BogdanBackend/Diplom/docs/ch4.md

# ЕКСПЕРИМЕНТАЛЬНЕ ВИПРОБУВАННЯ

У цьому розділі представлено практичні випробування, проведені з метою перевірки працездатності та ефективності використання програмно-визначеного радіо (SDR) для прийому та обробки радіосигналів у реальних умовах. Основна увага зосереджена на експериментах, які демонструють можливості сучасних SDR-приймачів і програмних засобів прийому та обробки аналогових і супутникових сигналів.

Використання гнучких програмно-апаратних платформ дає змогу реалізовувати прийом, фільтрацію, демодуляцію та збереження сигналів без потреби у складному радіоелектронному обладнанні. Такий підхід відкриває нові перспективи для навчання, досліджень і прикладних завдань, пов’язаних з аналізом радіочастотного спектра.

У рамках випробувань було реалізовано два експерименти: прийом аналогового сигналу за допомогою портативної рації та SDR-приймача, а також дистанційний прийом супутникового зображення за допомогою онлайн-сервісу WebSDR. Обидва сценарії показують, як за допомогою доступних інструментів можна реалізувати повноцінну систему радіоприйому, обробки та візуалізації сигналу.

<!-- подяка автору https://www.youtube.com/watch?v=IaThnn2r1no -->

## Прийом аналогового радіосигналу за допомогою портативної рації та SDR-приймача

Мета роботи: Дослідити процес прийому та обробки аналогового радіосигналу за допомогою SDR-приймача BladeRF і програмного забезпечення GNU Radio, перевірити можливість його демодуляції, виводу на аудіосистему та запису у файл.

Теоретичні відомості

SDR — це радіоприймач, у якому більшість функцій (демодуляція, фільтрація, декодування) реалізовано програмно. Це дозволяє змінювати параметри прийому та обробки сигналу без зміни апаратного забезпечення.

Частотна модуляція (Frequency Modulation, FM) використовується для передавання звукових сигналів, при якій частота несучої хвилі змінюється пропорційно амплітуді вхідного сигналу. FM має високу стійкість до шумів, тому широко застосовується в аналоговому радіомовленні.

GNU Radio — програмне середовище для створення радіосистем на базі SDR. Працює з різними апаратними пристроями, зокрема BladeRF, і дозволяє створювати блок-схеми обробки сигналу.

Ми використовували портативну рацію Baofeng як джерело сигналу для експерименту. Основні технічні характеристики цієї рації такі: вона працює у діапазонах VHF (136–174 МГц) та UHF (400–520 МГц), забезпечує вихідну потужність від 1 до 8 Вт, використовує частотну модуляцію (FM) і дозволяє програмувати до 200 каналів. Також пристрій підтримує двоканальний моніторинг (Dual Watch), має функцію VOX для активації передавання голосом і оснащений системою шумоподавлення на основі CTCSS/DCS.

Використане обладнання та програмне забезпечення

* Джерело сигналу: портативна рація Baofeng
* Приймач: SDR-пристрій BladeRF
* Програмне забезпечення: GNU Radio

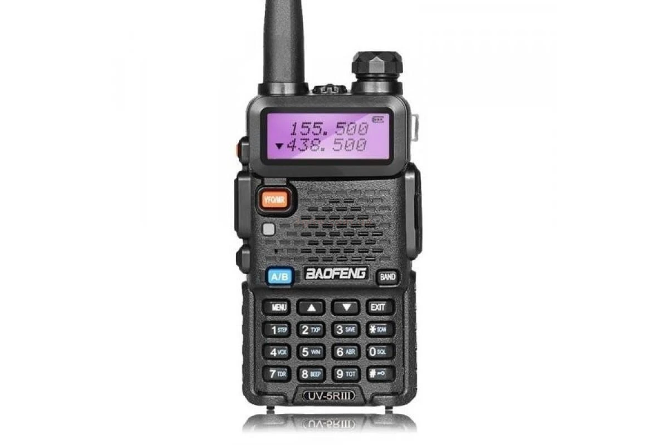
[picture p52: docs/imgs/image-35.png]
Рація Baofeng


Умови експерименту:

* Частота прийому: 446.13 МГц
* Частота дискретизації: задана у GNU Radio
* Посилення: мінімальне (–1)
* Вхідний блок: Osmocom Source (налаштований для BladeRF)

Блок-схема системи обробки сигналу:

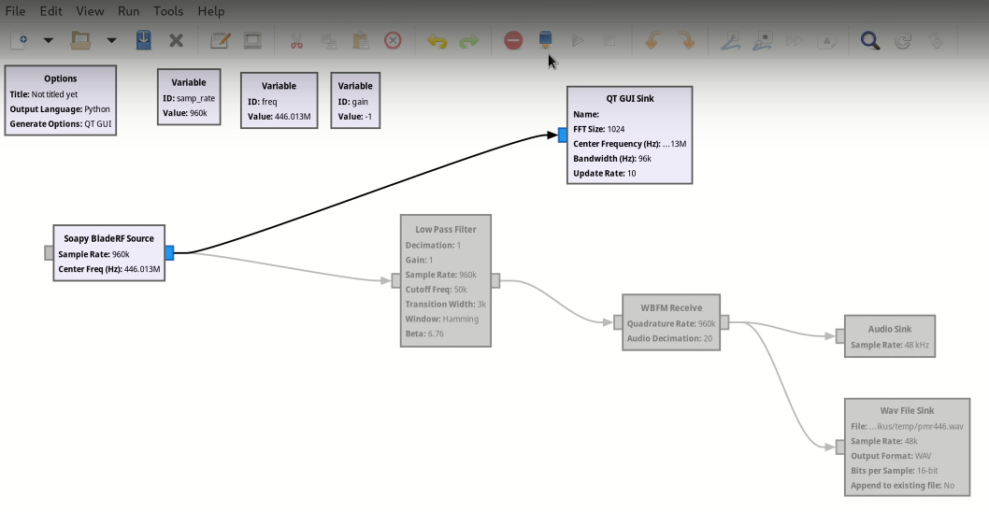
[picture p53: docs/imgs/image-36.png]
Структура цифрової обробки для графічного відображення


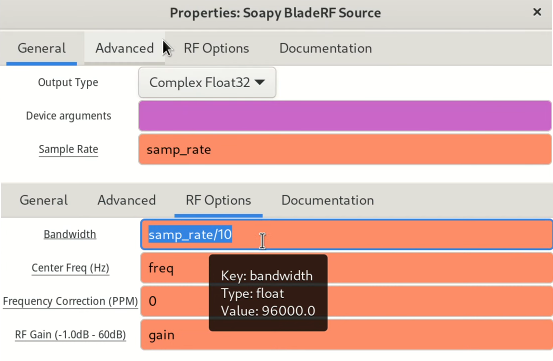
[picture p54: docs/imgs/image-37.png]
Параметри захоплення сигналу: частота, підсилення, ширина смуги пропускання


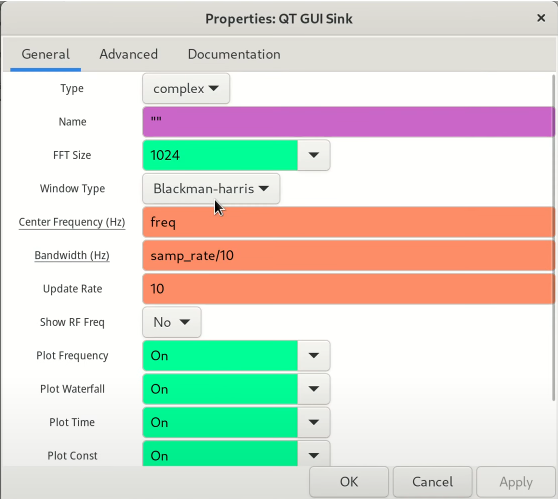
[picture p55: docs/imgs/image-38.png]
Параметри графічного відображення


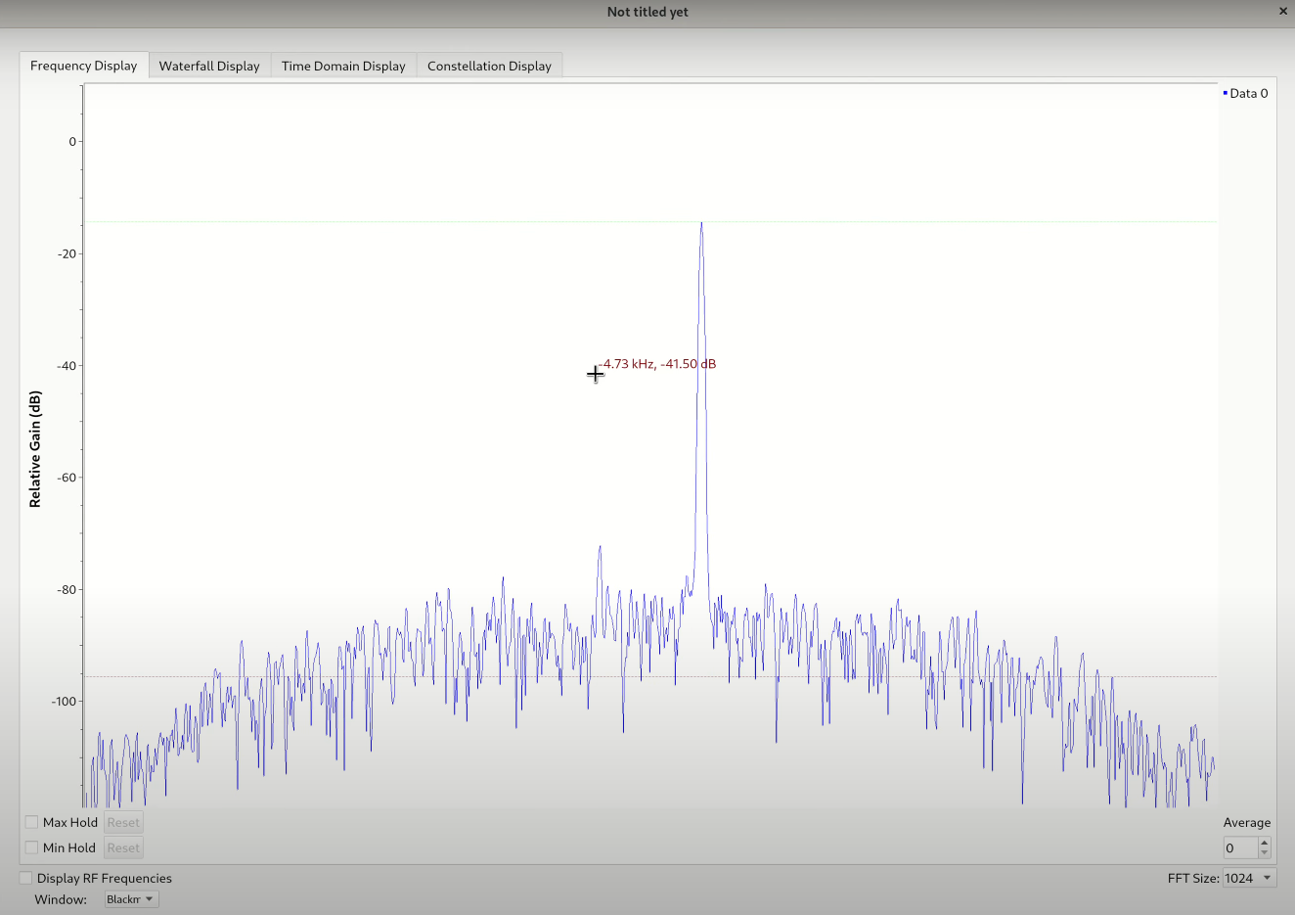
[picture p56: docs/imgs/image-39.png]
Спектр частот прийнятого сигналу


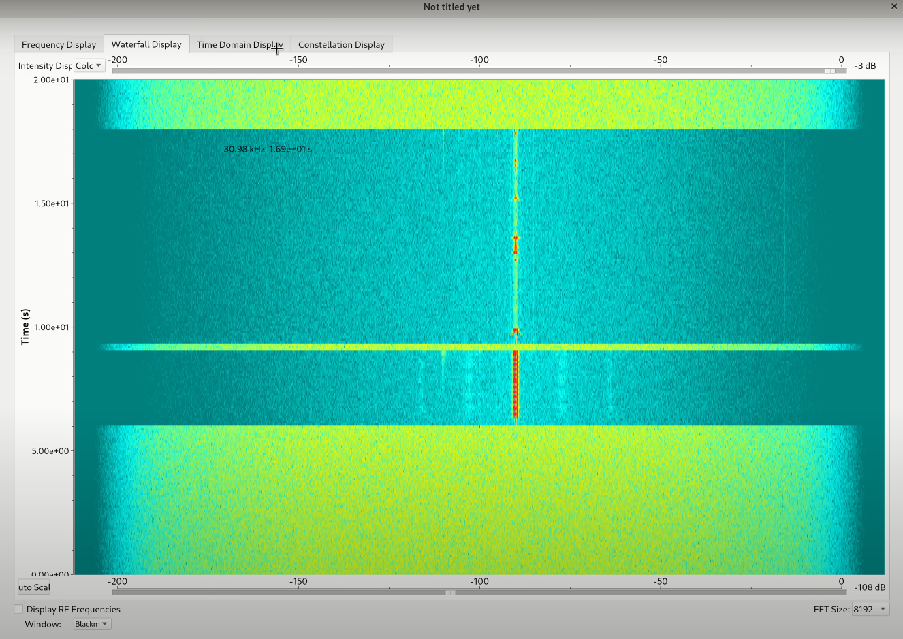
[picture p57: docs/imgs/image-40.png]
Динамічне водоспадне відображення прийнятого сигналу


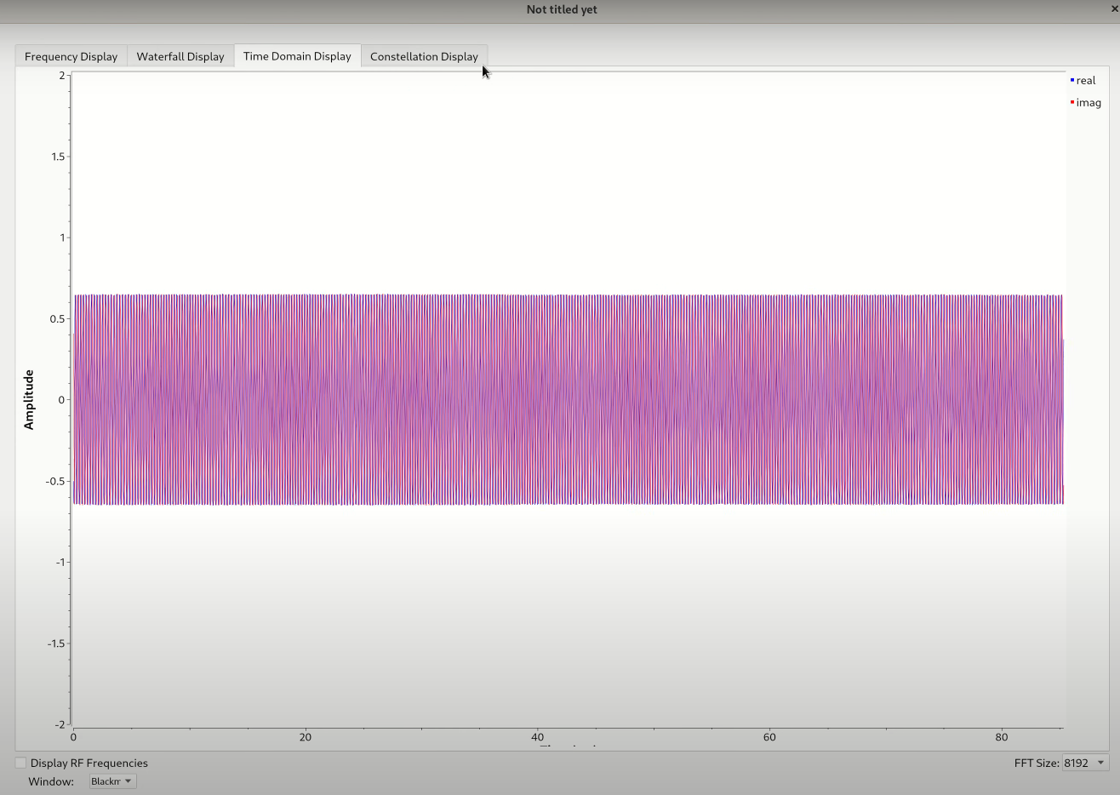
[picture p58: docs/imgs/image-41.png]
Амплітудне відображення прийнятого сигналу


<!-- ![Сузір’я прийнятого сигналу](imgs/image-42.png) -->

У процесі експерименту ми реалізували виведення сигналу на аудіосистему комп’ютера. Для цього до блок-схеми було додано фільтр низьких частот із частотою зрізу 50 кГц і перехідною зоною 3 кГц, блок демодуляції WBFM Receive із налаштуванням частоти дискретизації відповідно до потоку та параметром Audio Decimation, а також блок Audio Sink із частотою дискретизації 48000 Гц. Така конфігурація дала змогу якісно відтворити демодульований аудіосигнал у реальному часі.

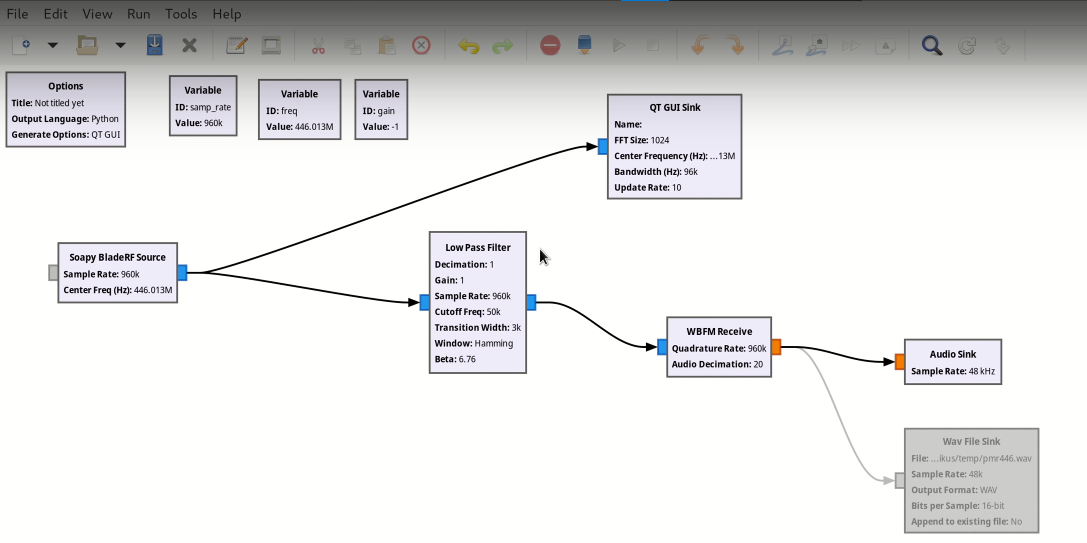
[picture p59: docs/imgs/image-43.png]
Структура цифрової обробки для аудіовиходу


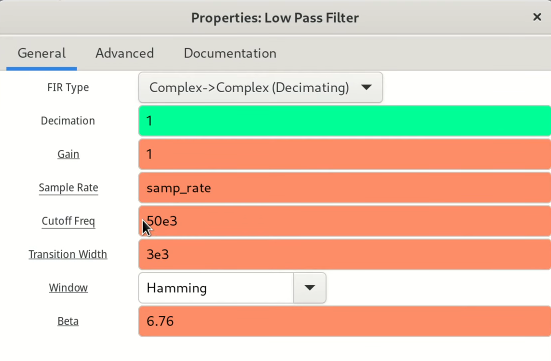
[picture p60: docs/imgs/image-44.png]
Налаштування фільтра низьких частот


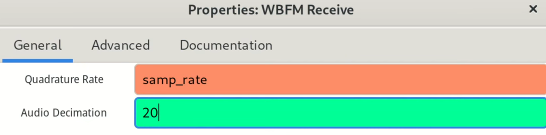
[picture p61: docs/imgs/image-45.png]
Налаштування FM демодулятора


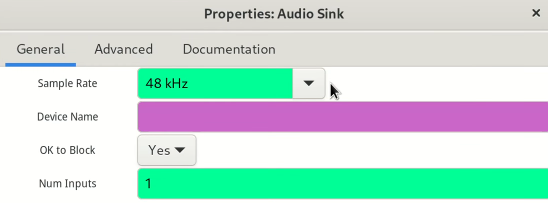
[picture p62: docs/imgs/image-46.png]
Налаштування аудіовиходу


Запис сигналу у WAV-файл ми здійснили шляхом заміни блоку Audio Sink на WAV File Sink у схемі обробки. Для цього встановили частоту дискретизації 48000 Гц, обрали монофонічний режим (1 канал) та формат WAV. Такий підхід дозволив нам зберегти демодульований аудіосигнал у зручному для подальшого аналізу та прослуховування вигляді.

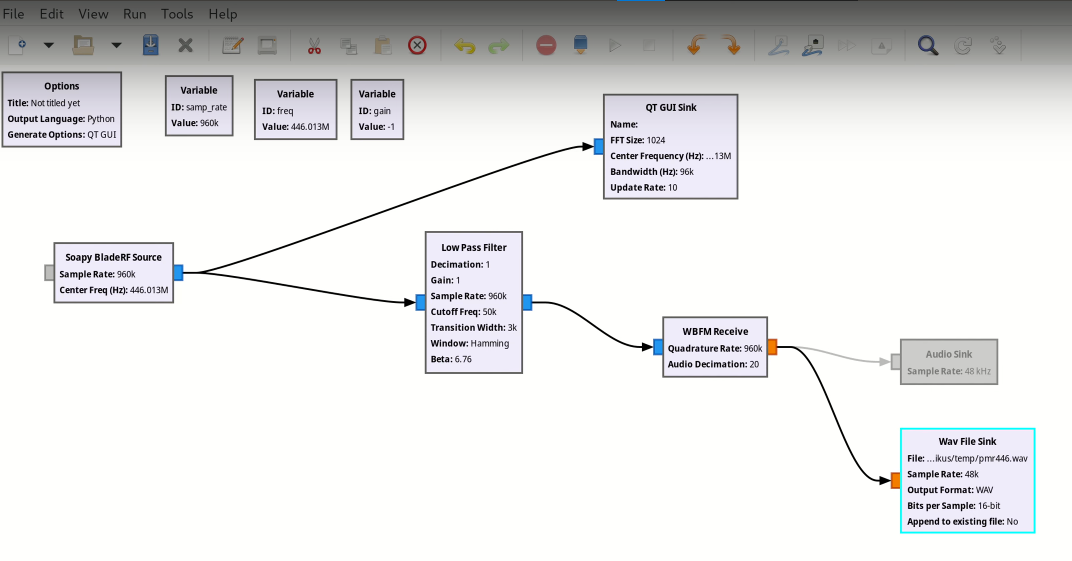
[picture p63: docs/imgs/image-47.png]
Структура цифрової обробки для запису


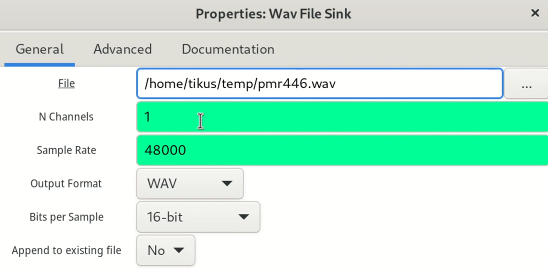
[picture p64: docs/imgs/image-48.png]
Налаштування блоку запису


Висновки

У результаті виконання експерименту ми реалізували прийом аналогового FM-сигналу за допомогою SDR-приймача BladeRF, провели спектральний аналіз сигналу та його графічне відображення, демодулювали і вивели аудіосигнал на звукову підсистему комп’ютера, а також виконали запис сигналу у файл формату WAV.

Отримані результати підтверджують функціональність та ефективність використання SDR-технологій у задачах аналізу аналогових радіосигналів, а також демонструють широкі можливості GNU Radio як програмної платформи для цифрової обробки сигналів.

<!-- дякую https://www.youtube.com/watch?v=cjClTnZ4Xh4 -->

## Прийом супутникових зображень

Мета роботи: Отримати супутникові зображення шляхом дистанційного прийому сигналів з метеорологічних супутників NOAA за допомогою WebSDR та ПЗ демодуляції.

Використане обладнання та програмне забезпечення

Обладнання:

[WebSDR](http://websdr.org/): онлайн-приймач, який дозволяє приймати сигнали метеорологічних супутників.
Обрано WebSDR з антеною Double Cross з круговою поляризацією для покращення якості прийому.

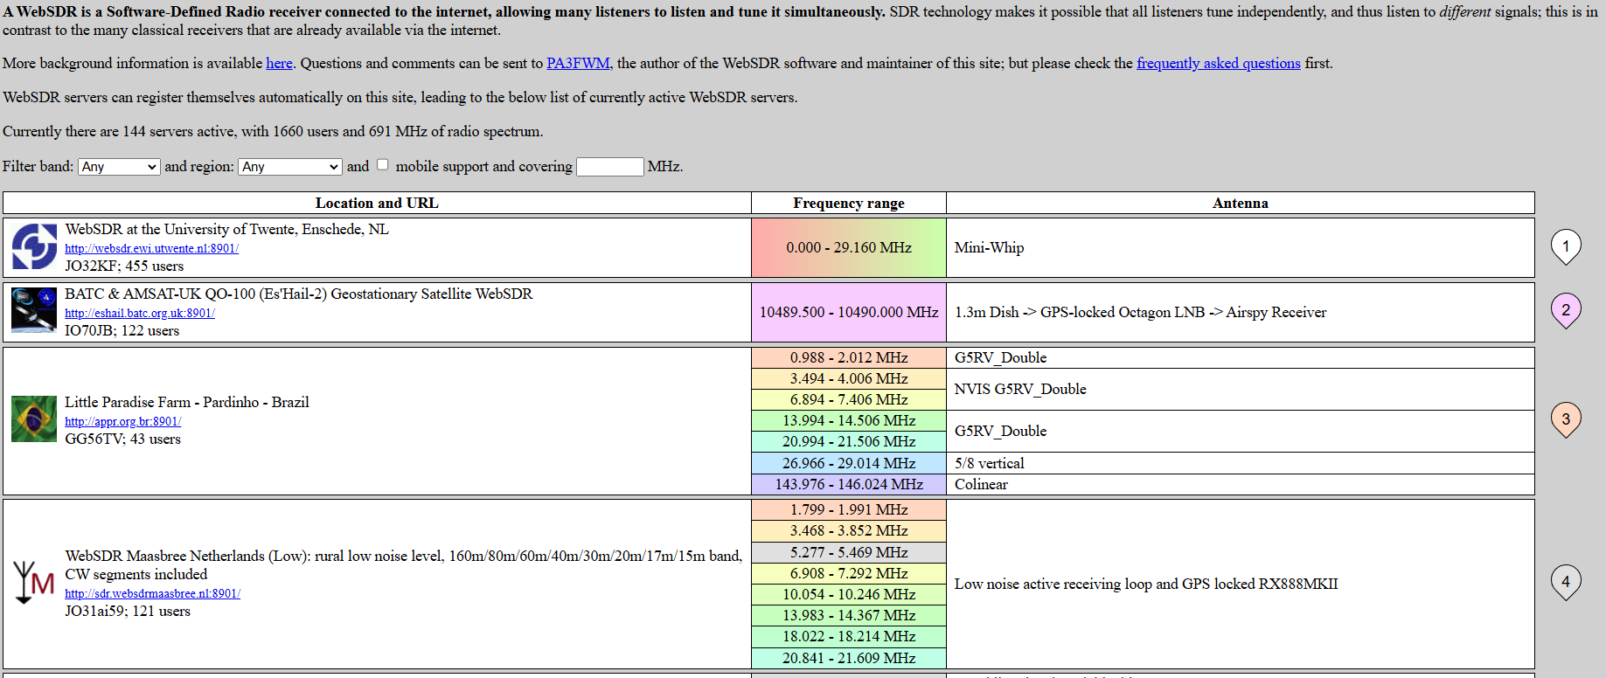
[picture p65: docs/imgs/image-49.png]
WebSDR ресурс онлайн SDR


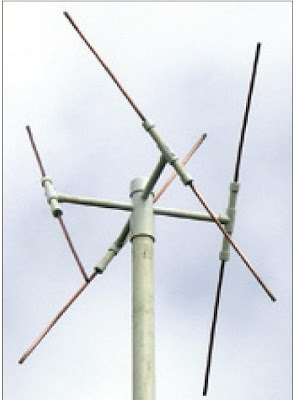
[picture p66: docs/imgs/image-51.png]
Антена Double Cross


Програмне забезпечення:

* SDR# (SDRSharp): використовується для обробки аудіофайлу та його конвертації.
* [LRPTDecoder](https://www.rtl-sdr.com/m2_lrpt_decoder-version-59-released/): декодує супутникові зображення з сигналу.
* Orbitron / Gpredict: для прогнозування проходження супутників над місцем прийому.
* [VB-Cable](https://vb-audio.com/Cable/): віртуальний аудіокабель для перенаправлення аудіо з браузера до інших програм.

Супутники:

* [NOAA 15, 18, 19](https://uk.wikipedia.org/wiki/NOAA-19): метеорологічні супутники з аналоговою та цифровою передачею даних.

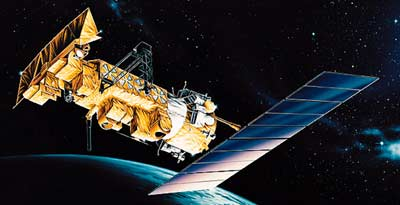
[picture p67: docs/imgs/image-50.png]
Супутник NOAA


Хід експерименту

Підключення до WebSDR та захоплення сигналу

Відповідний WebSDR з прийомом у діапазоні 137 МГц знайдено через пошук за запитами “WebSDR NOAA Meteor”.
За допомогою Orbitron введено координати для NOAA-15/18/19. Програма показує точний час проходження супутника.

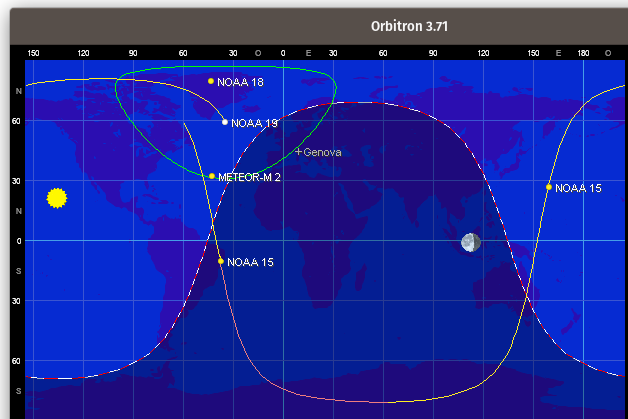
[picture p68: docs/imgs/image-52.png]
Orbitron - ПЗ відстеження супутників


Ми налаштували WebSDR, заздалегідь встановивши частоту 137.9125 МГц та режим NFM для прийому сигналу NOAA. Для супутників Meteor (наприклад, M2) обрали режим WFM або IQ-запис, якщо це підтримується сервісом. Під час проходження супутника здійснили запис сигналу: або через вбудовану функцію WebSDR (за наявності), або за допомогою VB-Cable, перенаправивши аудіо з браузера до програми Audacity для подальшої обробки. Після цього завантажили отриманий файл у LRPTDecoder, де запустили процес демодуляції. Програма обробила сигнал і сформувала супутникове зображення.

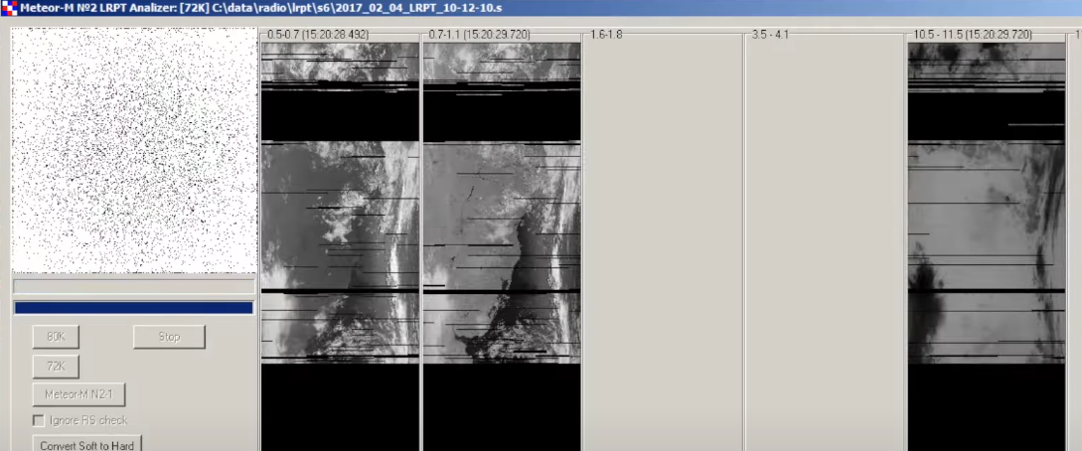
[picture p69: docs/imgs/image-54.png]
Декодований сигнал у LRPTDecoder


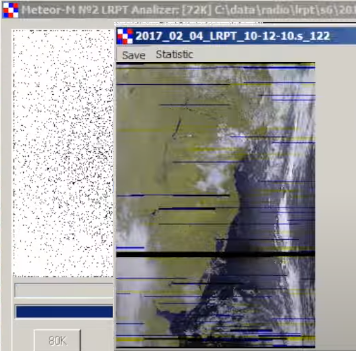
[picture p70: docs/imgs/image-55.png]
Результат декодування в RGB


Висновки

У результаті експерименту ми успішно підключилися до WebSDR, прийняли супутниковий сигнал, здійснили його запис у форматі, придатному для подальшої обробки, а також декодували супутникове зображення за допомогою LRPTDecoder.

Експеримент підтвердив можливість дистанційного прийому супутникових зображень без необхідності фізичного SDR-приймача. Інтеграція WebSDR з програмними інструментами для декодування дозволяє навіть аматорам ефективно працювати з даними метеорологічних супутників. Це відкриває широкі можливості для досліджень у сфері супутникової метеорології та радіозв’язку.

## Висновок по розділу 4

У цьому розділі було розглянуто практичні аспекти роботи з SDR (Software Defined Radio) для прийому та обробки аналогових і супутникових радіосигналів. Проведені експерименти показали, що SDR-платформи забезпечують гнучкість, універсальність і доступність для дослідників та аматорів. Використання сучасного програмного забезпечення дозволяє не лише приймати сигнали, а й виконувати їхню демодуляцію, декодування та подальшу обробку. Таким чином, SDR-технології відкривають широкі можливості для експериментів у сфері радіозв'язку, навчання та досліджень, а також сприяють популяризації радіоелектроніки серед широкого кола користувачів.
