BogdanBackend/Diplom/docs/0.md

<!-- 
---

---

> TODO розкидати ТЗ

----- РОЗРОБКА ТЕХНІЧНОГО ЗАВДАННЯ
Розробити Прилад, котрий дасть можливість отримати безпосередні дані задетектованих частот та амплітуд, які можуть бути використані для розрахунку балістичної траєкторії фізичних об'єктів. Моніторинг та управління дронами. (яких об'єктів ????)  та планування операцій (яких операцій ????) Для моніторингу фізичних об'єктів, що випромінюють радіосигнал (дронів, рацій, радіостанцій, станцій керування радіо об'єктами та інш.)

1. Загальні вимоги:
    * Розробити планшетний комп'ютерний комплекс (КПК).  
    * Забезпечити автономність роботи приладу протягом не менше 3-х годин.  
    * Забезпечити роботу при високій вологості, захист від пилу та зовнішніх впливів згідно зі стандартом IP44.  
    * Дотримати вимоги ергономіки та компактності для зручного використання у польових умовах.

2. Апаратна складова:

   1. Центральний модуль:
        * Процесор ARM Cortex-A72.  
        * Графічний процесор VideoCore VI.  
        * Оперативна пам’ять LPDDR4-3200 SDRAM.  
        * Флеш-накопичувач обсягом від 16 ГБ.
   2. Інтерфейси:
        * Порт USB.  
        * Порт HDMI для підключення зовнішнього монітора.  
        * Роз’єм Ethernet для дротового підключення до мережі.  
        * Слот для карт microSD.  
        * Порт USB Type C PD.
   3. Енергозабезпечення:
        * Акумулятор ємністю не менше 100 Вт\*год.  
        * Можливість заряджання приладу від автомобільного акумулятора (12/24 В).  
        * Можливість заряджання від USB Type C PD.
   4. Дисплей:
        * Вмонтований сенсорний екран діагоналлю 10 дюймів з роздільною здатністю HD (1024x768 пікселів).  
        * Зовнішній HDMI екран 4K 60р (3840×2160  60 кадр/с).

3. Програмне забезпечення:

    * Підтримка SDRangle.  
    * Операційна система Linux.

4. Можливості:

Детектування та аналіз радіосигналів з частотою від 1 МГц до 6 ГГц. На екрані дисплею будуть відображені:

1. Спектр сигналу (Spectrum View)

Частота по горизонталі, амплітуда по вертикалі.

Дозволяє бачити, на яких частотах присутні сигнали.

Аналог осцилографа у частотній області (спектроаналізатор).

2. Водоспад (Waterfall View)

Графік, який показує зміну спектру сигналу з часом.

Кольори вказують інтенсивність сигналу.

Дуже корисно для виявлення короткочасних або періодичних сигналів.

3. Модуляція сигналу (IQ View / Demodulated Signal)

Виводить графіки фази та амплітуди сигналу.

Дає змогу бачити структуру модуляції

Показує форму хвилі в часі, схожу на осцилограму.

4. Протокольний аналіз (Protocol Decoding)

У графічному вигляді або як таблиця — розшифровані пакети протоколів.

Передача радіосигналів з частотою від 1 МГц до 6 ГГц. (Керування різноманітними пристроями, передача звукових повідомлень, повідомлень азбукою Морзе, передача закодованих повідомлень).

Відображення геопросторових даних: довготи, широти точки моніторингу. (При наявності направлених антен і вказання їх напрямку буде відображена приблизна геопозиція джерела прийнятого сигналу).

Відображення позиційного часу точки моніторингу.

Відображення геодезичної висоти точки моніторингу.

Відображення аналогового відео сигналу (перегляд FPV трансляції).

Відображення проаналізованих даних на зовнішньому HDMI дисплеї.

Заряджання сторонніх приладів USB 5В 1А.

запис відео на власні носії (SSD та microSD) та на інші носії USB 2.0 (3.0)

перегляд записаного відео з власних носіїв (SSD та microSD) та з інших носіїв на вмонтованому екрані чи на підключеному моніторі.

5. Експлуатаційні вимоги:
    * Робота у температурному діапазоні від \-10 °C до \+40 °C.  
    * Захист від механічних пошкоджень.  
    * Портативність для транспортування та оперативного розгортання.  
    * IP44 – захист від крапель та частинок \>1мм.

6. Очікувані результати:
    * Можливість роботи в польових умовах.  
    * Зниження ризиків за рахунок використання відкритих технологій та систем кіберзахисту.

---------- Висновок по розділу

Розробка технічного завдання для планшетного комп'ютерного комплексу є важливим етапом у створенні сучасного рішення для забезпечення ефективного управління артилерійськими підрозділами. Запропоновані технічні та програмні вимоги спрямовані на досягнення високої автономності, надійності та функціональності пристрою в умовах бойових дій. Інтеграція передових технологій, таких як моніторинг дронів, аналіз радіосигналів та балістичні розрахунки, дозволить значно підвищити оперативність і точність виконання завдань. Впровадження цього комплексу сприятиме підвищенню боєздатності підрозділів та забезпеченню їхньої ефективної роботи в реальному часі.

---

--- -->
