BogdanBackend/Diplom/docs/practical/2.md

### Тиждень 2. Дослідження технологій, що застосовуються в Інституті

Протягом другого тижня проходження практики було зосереджено увагу на вивченні науково-технічного потенціалу Інституту проблем міцності ім. Г.С. Писаренка НАН України. Інститут є однією з провідних установ в Україні та Східній Європі, яка проводить фундаментальні та прикладні дослідження в галузі механіки деформівного твердого тіла, аналізу міцності матеріалів і конструкцій за складних умов експлуатації.

Основні напрями досліджень включають аналіз міцності матеріалів при впливі високих (до 3000 К) і низьких (до 4 К) температур, агресивних середовищ, радіаційного опромінення, високочастотного втомного навантаження, ударів та імпульсів. Особлива увага приділяється вивченню повзучості, термовтоми, тріщиностійкості та визначенню залишкового ресурсу матеріалів і конструкцій, що експлуатуються в екстремальних умовах.

Інститут володіє унікальною експериментальною базою, яка дозволяє проводити дослідження на високому науковому рівні. Серед основного обладнання:

* Газодинамічні стенди для випробування зразків у потоці гарячого газу з температурою до 2700 К;
* Високотемпературні печі для дослідження жароміцних матеріалів;
* Печі з радіаційним, індукційним і електрострумовим нагрівом;
* Пневмопорохові копри для імітації імпульсних навантажень на швидкостях до 1000 м/с;
* Стенди серії «Нейтрон» — для випробувань у середовищі радіаційного опромінення;
* Установки для кріогенних випробувань з температурою до 4 К;
* Машини для циклічного навантаження (мало- та багатоциклове втомне навантаження);
* Ультразвукові та акустичні системи для неруйнівного контролю.

Разом з фізичними експериментами в Інституті широко застосовуються методи комп’ютерного моделювання. Використовується як комерційне, так і власне програмне забезпечення для розрахунку міцності та деформування матеріалів і елементів конструкцій.

Серед комерційного ПЗ, що активно застосовується:

* [SolidWorks Simulation](https://www.solidworks.com/product/solidworks-simulation) – для статичного та динамічного аналізу механічних навантажень, створення 3D-моделей конструкцій, включаючи корпуси пристроїв;
* [ANSYS](https://www.ansys.com/) – для аналізу напружено-деформованого стану, теплових полів, втоми, стійкості, багатофізичних процесів;
* [MathCAD](https://mathcad.com.ua/) – для аналітичних розрахунків і обробки експериментальних даних;
* [COMSOL Multiphysics](https://www.comsol.com/) – для багатофізичних задач, що поєднують механіку, теплопровідність, електричні впливи.

Крім того, в Інституті існує низка власних програмних розробок, створених для специфічних задач міцності, які враховують особливості матеріалів, багатокомпонентні навантаження, а також нестабільність або розсіювання властивостей у реальних умовах експлуатації. Деякі з цих програм мають модулі для розрахунку залишкового ресурсу деталей машин та прогнозування граничних станів.

Комбінація фізичних випробувань та чисельного аналізу забезпечує високу точність досліджень і дозволяє ефективно розробляти нові конструкції з урахуванням усіх експлуатаційних ризиків. Саме такі підходи становлять методологічну основу, що може бути застосована при розробці корпусу портативного пристрою для виявлення та аналізу радіосигналів, що експлуатуватиметься в умовах впливу механічних, вібраційних і температурних навантажень.
