BogdanBackend/Diplom/docs/practical/3.md

# Тиждень 3. Доцільність вибраних технологій у проєктуванні корпусу відповідно до норм Інституту

На третьому тижні практики було зосереджено увагу на аналізі можливих конструктивних і матеріальних рішень для корпусу автоматизованого портативного комплексу виявлення та аналізу радіосигналів. З урахуванням призначення пристрою та вимог технічного завдання (робота у температурному діапазоні від -20 °C до +50 °C, захист за стандартом IP65, стійкість до механічних впливів, вібрацій, пилу, вологи, а також автономна робота до 20 годин) було розглянуто декілька варіантів матеріалів корпусу.

## Порівняльний аналіз кандидатів на матеріал корпусу:

1. Пластики технічного призначення ([ABS, PC, ABS+PC, Nylon](https://plasticextrusiontech.net/)):

Переваги:

* Мала маса.
* Простота лиття й виготовлення.
* Висока ударна в’язкість (особливо у полікарбонату).
* Добра діелектрична ізоляція.

Недоліки:

* Обмежена термостійкість (не всі витримують 50 °C без деформацій).
* Менша жорсткість порівняно з металами.
* Зниження механічних властивостей під час старіння або впливу УФ.
* Складніше забезпечити ефективне тепловідведення.
* Менша стійкість до агресивного середовища, порівняно з металами.

2. [Композиційні матеріали](https://www.products.pcc.eu/uk/blog/якими-властивостями-володіє-скловол) (скловолоконні або вуглепластики):

Переваги:

* Дуже висока міцність при малій вазі.
* Стійкість до корозії.
* Можливість оптимізації під конструктивні задачі.

Недоліки:

* Висока вартість.
* Складність механічної обробки та ремонту.
* Проблеми з герметизацією отворів, кріплень, швів.
* Обмежена ударостійкість деяких видів при локальному навантаженні.

3. Алюмінієві сплави (наприклад, [6061-T6](https://asm.matweb.com/search/specificmaterial.asp?bassnum=ma6061t6), [5052-H32](https://www.matweb.com/search/datasheet.aspx?MatGUID=96d768abc51e4157a1b8f95856c49028&ckck=1)):

Переваги:

* Висока питома міцність і жорсткість.
* Хороша термостійкість і теплопровідність (перевага для радіоелектроніки).
* Добра корозійна стійкість, особливо після анодування.
* Придатність для герметичного складання корпусу з ущільненням.
* Висока ремонтопридатність, легкість у механічній обробці.

Недоліки:

* Дещо більша маса, ніж у пластиків.
* Порівняно вища вартість

З огляду на порівняльний аналіз, оптимальним вибором для основної частини корпусу визнано алюмінієвий сплав 6061-T6. Цей матеріал забезпечує необхідний баланс між міцністю, термостійкістю, оброблюваністю та масою. Він добре піддається фрезеруванню, свердлінню, шліфуванню й анодуванню, що дозволяє не лише точно реалізувати геометрію корпусу, а й додатково захистити поверхню від корозії та зносу.

## Вибір матеріалу для кришки дисплея:

Для прозорої кришки дисплея було проаналізовано два основні варіанти: мінеральне (загартоване) скло та органічне скло ([PMMA](https://www.pmma-online.eu/pmma-science/properties-and-benefits/), або поліметилметакрилат). З урахуванням необхідності зниження ваги, забезпечення антивідблискового покриття та достатньої механічної міцності, обрано органічне скло з УФ-захисним шаром.

Його переваги:

* Висока прозорість і стійкість до подряпин (після покриття).
* Менша вага — критично важливо для портативного комплексу.
* Ударостійкість, що перевищує властивості звичайного скла.
* Можливість герметичного кріплення до алюмінієвого корпусу із використанням ущільнювального силікону або гумового контуру.
* Доступність і легкість в обробці.

## Узгодження з нормами Інституту

Обрані матеріали — алюмінієві сплави та органічне скло — є широко досліджуваними в Інституті проблем міцності, з доступною експериментальною базою щодо їхньої поведінки в умовах ударного, вібраційного, статичного і термічного навантаження. Це дозволяє використати результати попередніх досліджень та методики симуляційного аналізу, які апробовані на відповідному випробувальному обладнанні.

Вибір матеріалів та попередній підхід до конструкції було узгоджено з науковим керівником практики, що дозволяє перейти до наступного етапу – розробки 3D-моделі корпусу в CAD-середовищі SolidWorks та підготовки до механічного моделювання.
