BogdanBackend/Diplom/docs/practical/0_plan.md

# План проходження практики

## Тиждень 1. Ознайомлення з Інститутом та його історією

* Вивчення історії створення та розвитку Інституту.
* Ознайомлення з основними напрямами наукової діяльності установи.
* Аналіз структури Інституту: наукові відділи, лабораторії, експериментальні бази.
* Вивчення внеску академіка Г.С. Писаренка та його наукової школи.
* Оформлення щоденника практики та первинних висновків щодо специфіки наукової установи.

## Тиждень 2. Дослідження актуальних технологій та методів, що застосовуються в Інституті

* Ознайомлення з сучасними підходами до аналізу міцності конструкцій в екстремальних умовах.
* Вивчення методів розрахунку граничних станів та деформування матеріалів.
* Ознайомлення з прикладним програмним забезпеченням (ANSYS, SolidWorks Simulation, Abaqus).
* Участь у демонстраційних випробуваннях або перегляд результатів досліджень, проведених на стендах Інституту.
* Вивчення методик експериментального моделювання для різних матеріалів (металів, полімерів, композицій тощо).

## Тиждень 3. Аналіз доцільності вибраних матеріалів та відповідність нормам Інституту

* Визначення вимог до корпусу пристрою з урахуванням умов експлуатації (механічні навантаження, температури, вібрації).
* Аналіз можливих конструктивних рішень з позиції міцності, жорсткості, герметичності.
* Вибір матеріалів для корпусу: алюміній, полімери або композити.
* Перевірка відповідності конструкції нормам та рекомендаціям, що діють в Інституті.
* Узгодження етапів розробки з науковим керівником практики.

## Тиждень 4. Проєктування корпусу пристрою

* Створення 3D-моделі корпусу в SolidWorks.
* Формування вимог до конструкції з урахуванням ергономіки, міцності та функціональності.
* Підготовка креслень, специфікацій та технічної документації.
* Проведення попередньої оцінки придатності конструкції до виробництва.
* Підготовка моделі до симуляційного аналізу.

## Тиждень 5. Механічний аналіз та тестування матеріалів

* Вивчення фізико-механічних властивостей алюмінію та обраного полімеру (ударна в’язкість, модуль пружності, межа міцності).
* Проведення комп’ютерного аналізу міцності (CAE-симуляцій) розробленого корпусу.
* Аналіз поведінки корпусу при падінні, вібрації, статичному навантаженні.
* Висновки щодо вибору матеріалу та геометрії корпусу з урахуванням практичних вимог.
* Підготовка звіту за результатами практики, оформлення додатків (моделі, графіки, симуляції).

## Підсумкові матеріали за результатами практики:

* Щоденник проходження практики.
* Технічний звіт про результати досліджень і розробки.
* 3D-модель корпусу пристрою з кресленнями.
* Висновки щодо вибору матеріалів і рекомендації щодо подальшого впровадження.
