BogdanBackend/Diplom/docs/practical/out/template/practiacal_template.docx

МІНІСТЕРСТВО ОСВІТИ Й НАУКИ

НАЦІОНАЛЬНИЙ ТЕХНІЧНИЙ УНІВЕРСИТЕТ УКРАЇНИ

«КИЇВСЬКИЙ ПОЛІТЕХНІЧНИЙ ІНСТИТУТ імені ІГОРЯ СІКОРСЬКОГО»

Приладобудівний факультет

Кафедра автоматизації та систем неруйнівного контролю

ЗВІТ

по виробничій практиці

на базі ……………….назва підприємства………………….

На тему………………………………………………………………….

Виконав

студент гр. ПМ-11 (КЕП, дата) Погорєлов Богдан

Київ 2025

Зміст

Вступ 3

# Вступ

вступ бла бла бла
