BogdanBackend/Diplom/msDocx/specification.pdf

Фор

мат
Зона
Пози

ція
Позначення | Найменування

Кількість
Примітка

Документація

A1 | ДР.ПМ-11.09.25.000 СК | Складальне креслення

Складальні одиниці

А1 | 7 | Материнська плата | 1
| | Деталі
А1 | 1 | ДР.ПМ-11.09.25.001 | Корпус | 1
А4 | 2 | ДР.ПМ-11.09.25.002 | Захисна кришка | 1
А4 | 5 | ДР.ПМ-11.09.25.003 | Захист екрану | 1

Стандартні одиниці

3 | Акамуляторна батарея | 1
4 | Радіо модуль | 1
6 | Роз’єм антени | 4
8 | Болт М3 10мм | 22
9 | Болт М3 5мм з | 2
| накатаною головкою

## ДР.ПМ-11.09.25.000 СП

ЗМ. | Арк.. | № докум. | Підпис | Дата
