BogdanBackend/Diplom/docs/imgs/image-11.png

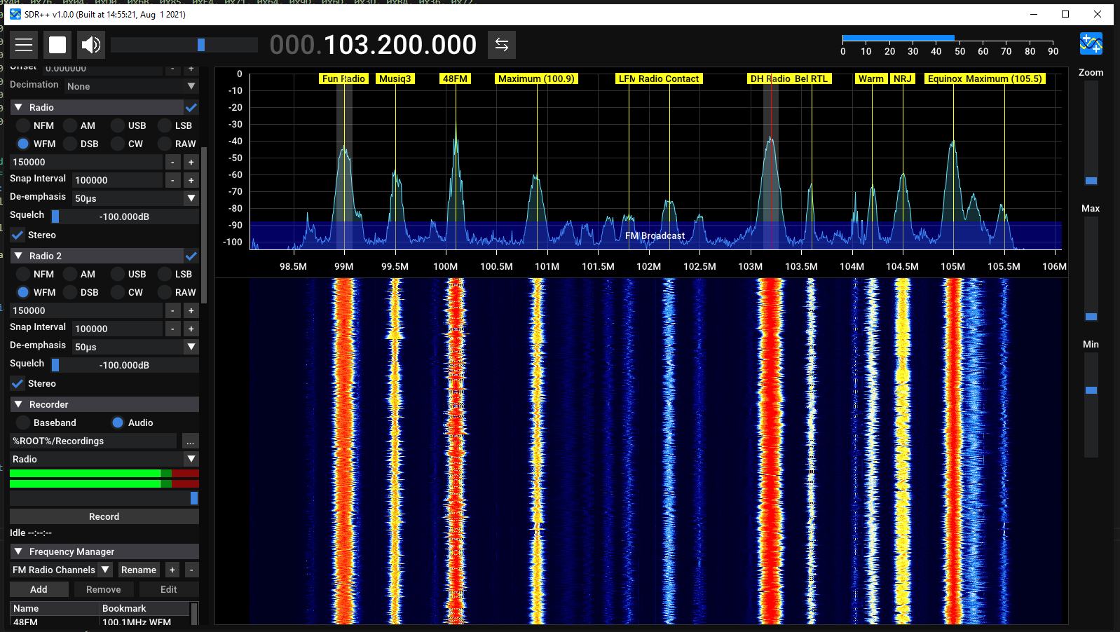
docs/imgs/image-11.png
