BogdanBackend/Diplom/docs/imgs/image-15.png

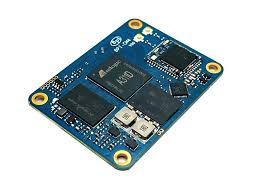
docs/imgs/image-15.png
