BogdanBackend/Diplom/docs/imgs/image-18.png

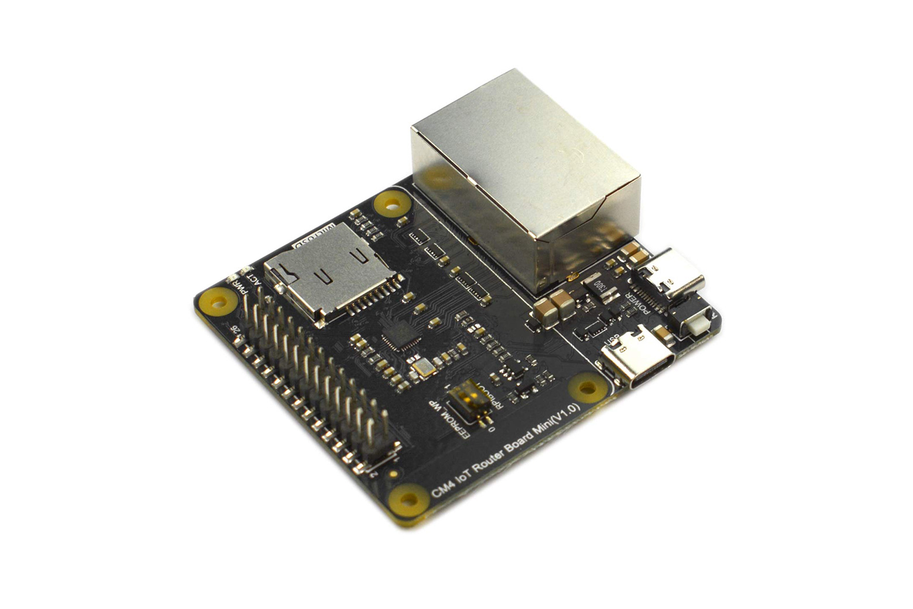
docs/imgs/image-18.png
