BogdanBackend/Diplom/docs/imgs/image-21.png

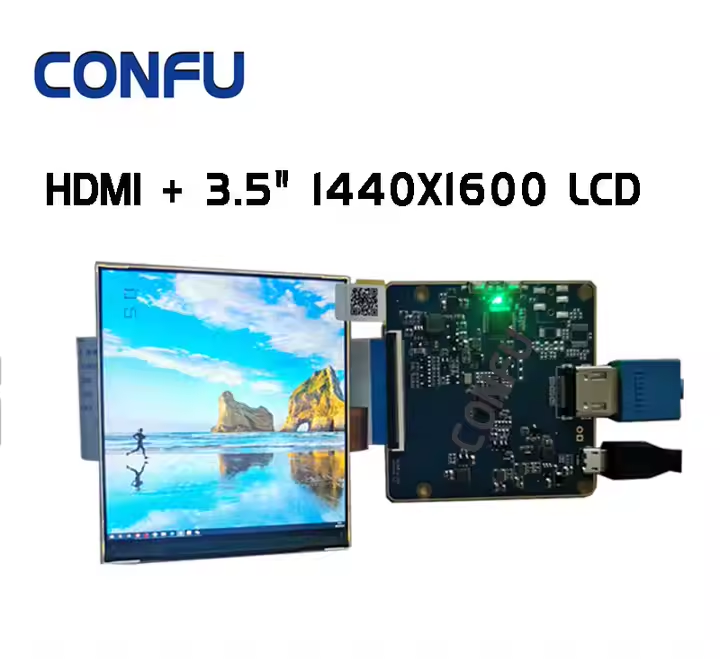
docs/imgs/image-21.png
