BogdanBackend/Diplom/docs/imgs/image-25.png

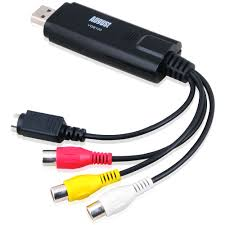
docs/imgs/image-25.png
