BogdanBackend/Diplom/docs/imgs/image-33.png

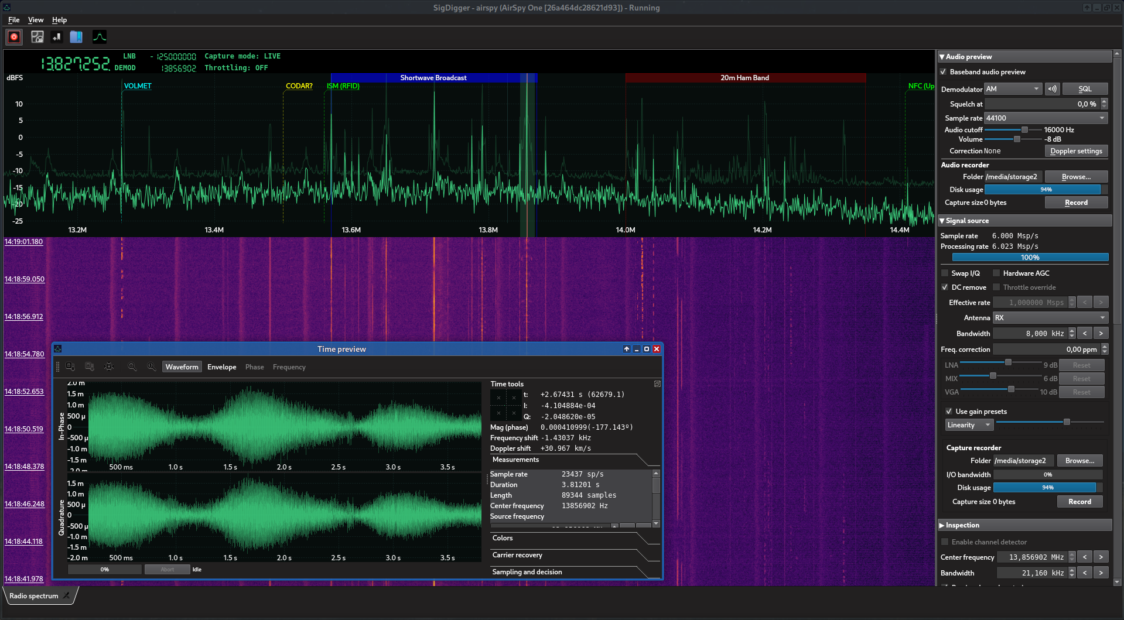
docs/imgs/image-33.png
