BogdanBackend/Diplom/docs/imgs/image-42.png

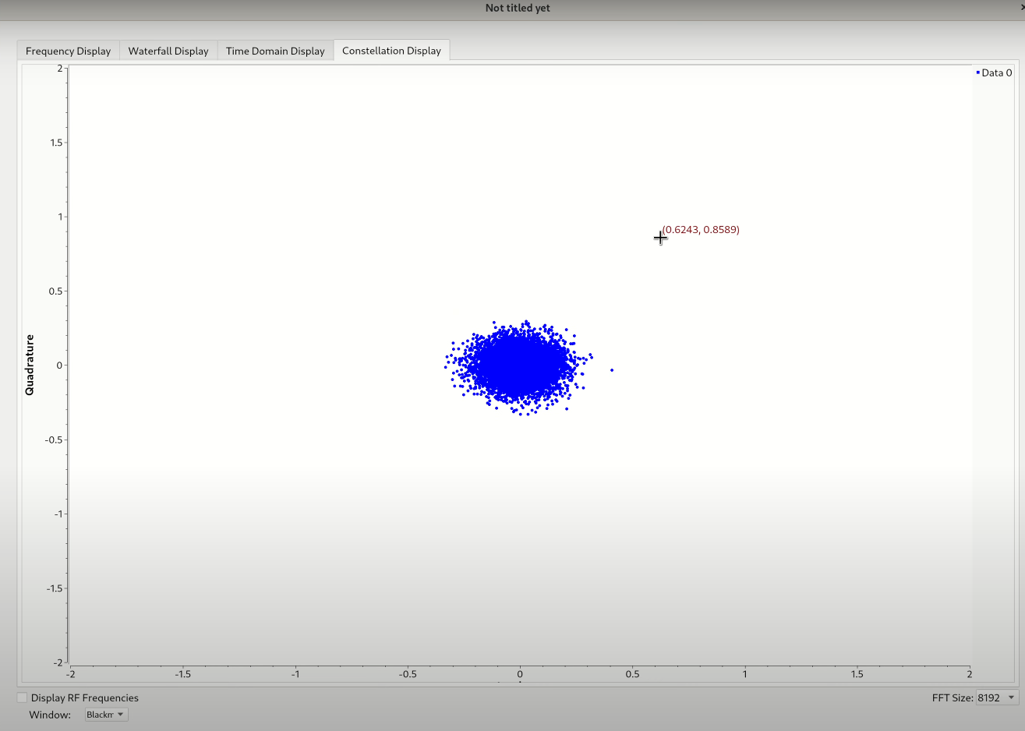
docs/imgs/image-42.png
