BogdanBackend/Diplom/docs/imgs/image-53.png

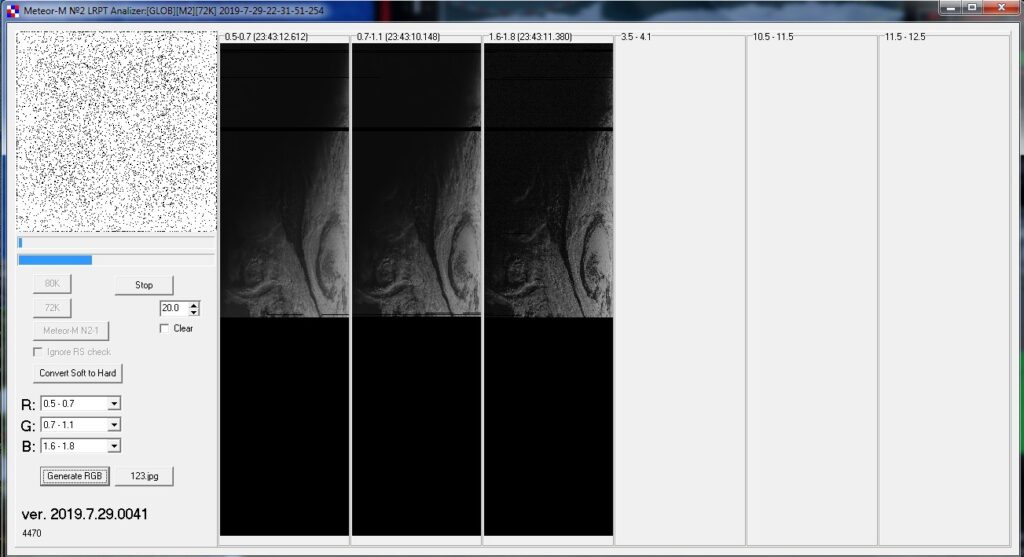
docs/imgs/image-53.png
