BogdanBackend/Diplom/docs/imgs/image-56.png

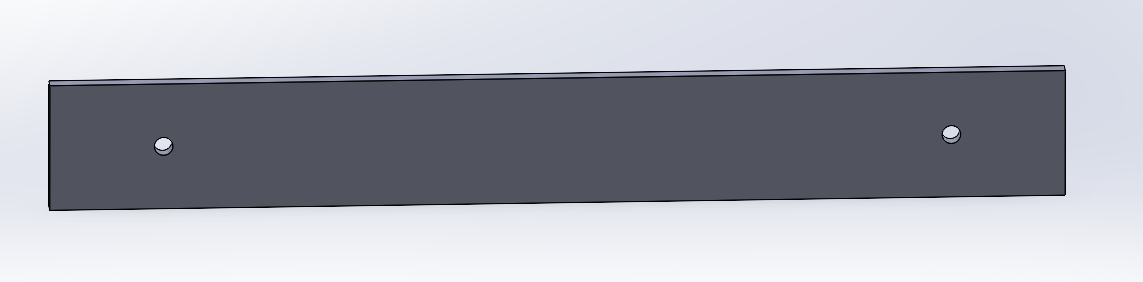
docs/imgs/image-56.png
