BogdanBackend/Diplom/docs/imgs/Solid/Cover.png

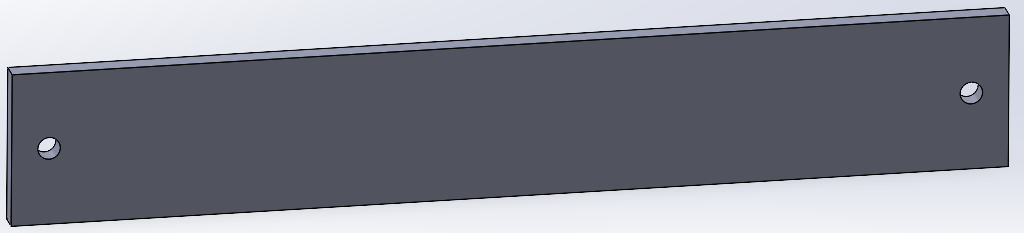
docs/imgs/Solid/Cover.png
