BogdanBackend/Diplom/docs/imgs/Solid/Top.png

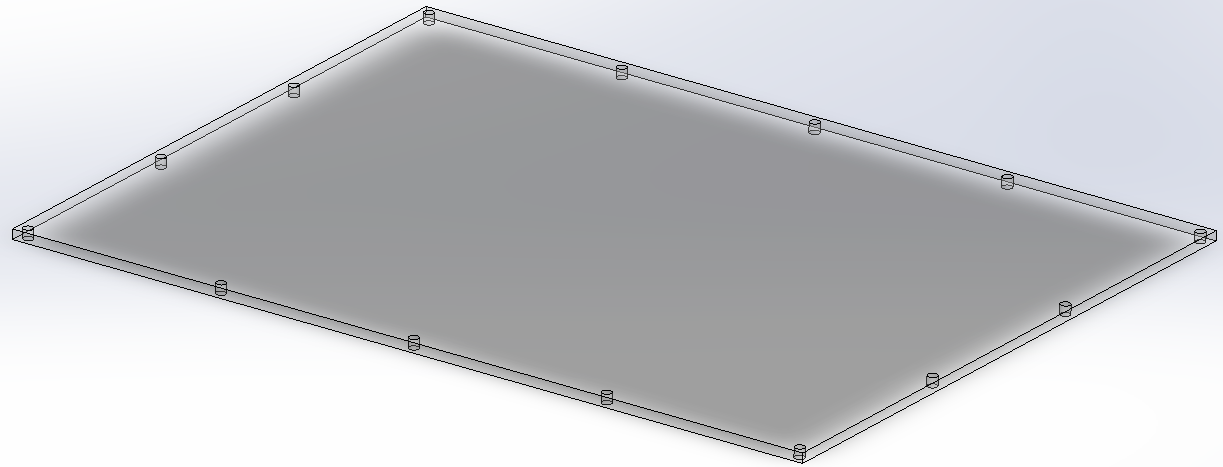
docs/imgs/Solid/Top.png
