BogdanBackend/Diplom/model/bladerf.png

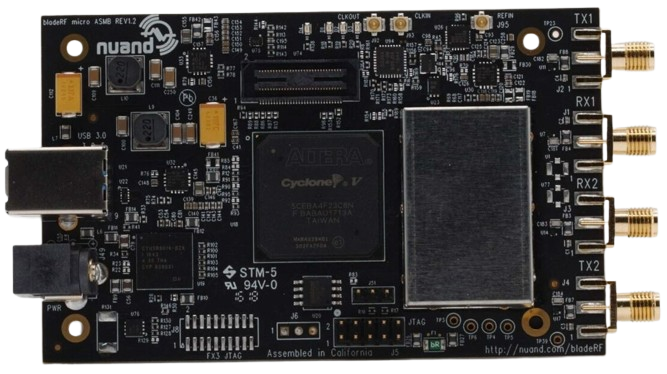
model/bladerf.png
