BogdanBackend/Diplom/model/bladerf_cut.png

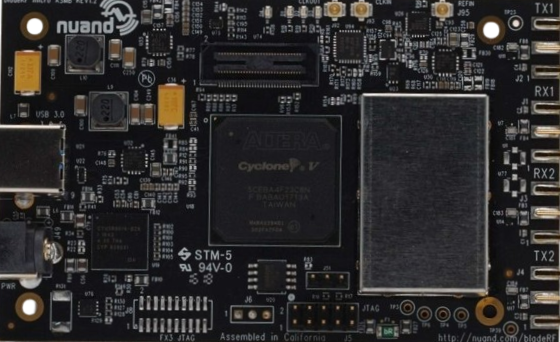
model/bladerf_cut.png
