BogdanBackend/Diplom/model/Top.pdf

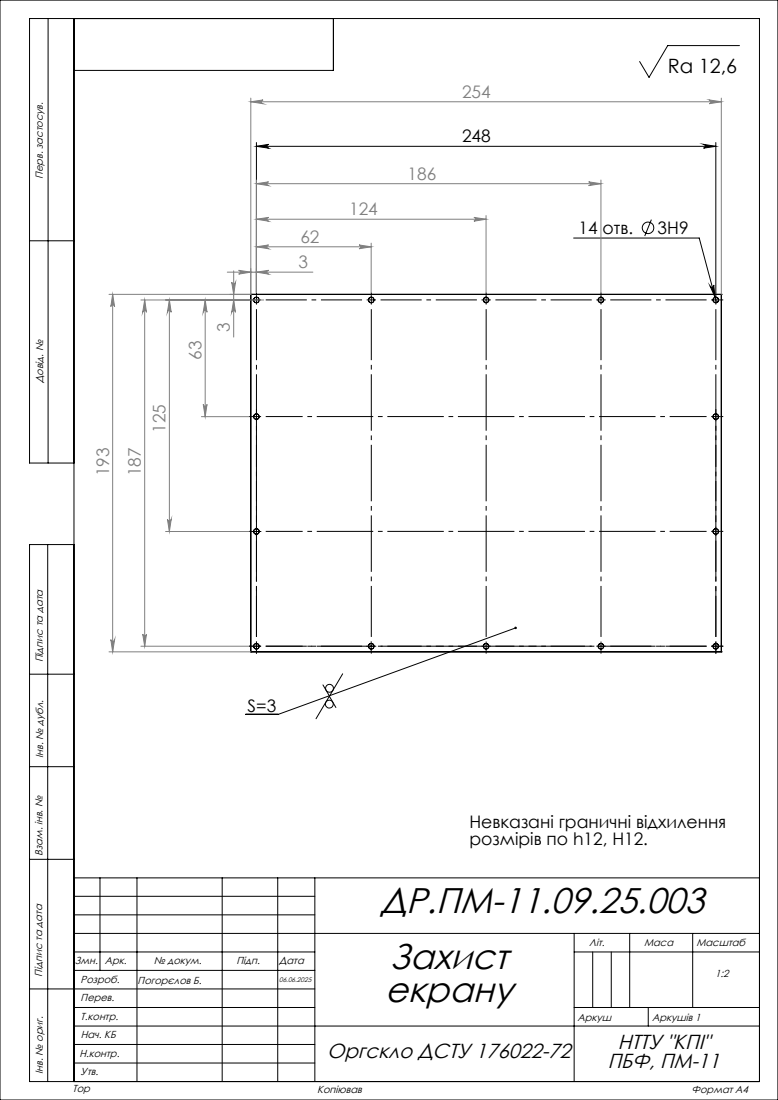
[picture p173: page 1]
14 отв. 3H9 62; 1:2 Погорєлов Б.; Копіював; Формат А4

Довід. № Перв. застосув.

Підпис та дата Інв. № дубл. Взам. інв. № Підпис та дата Інв. № ориг.

Невказані граничні відхилення
розмірів по h12, H12.

Захист екрану | Літ. | Маса | Масштаб

Змн. Арк. | № докум. | Підп. | Дата

Розроб. | | | 06.06.2025
Перев.
Т.контр. | | | | Аркуш | Аркушів 1
Нач. КБ | | | Оргскло ДСТУ 176022-72 | НТТУ "КПІ" ПБФ, ПМ-11
Н.контр.
Утв.
