BogdanBackend/Diplom/motherBoard/Out/pcb/CM5IO.pdf

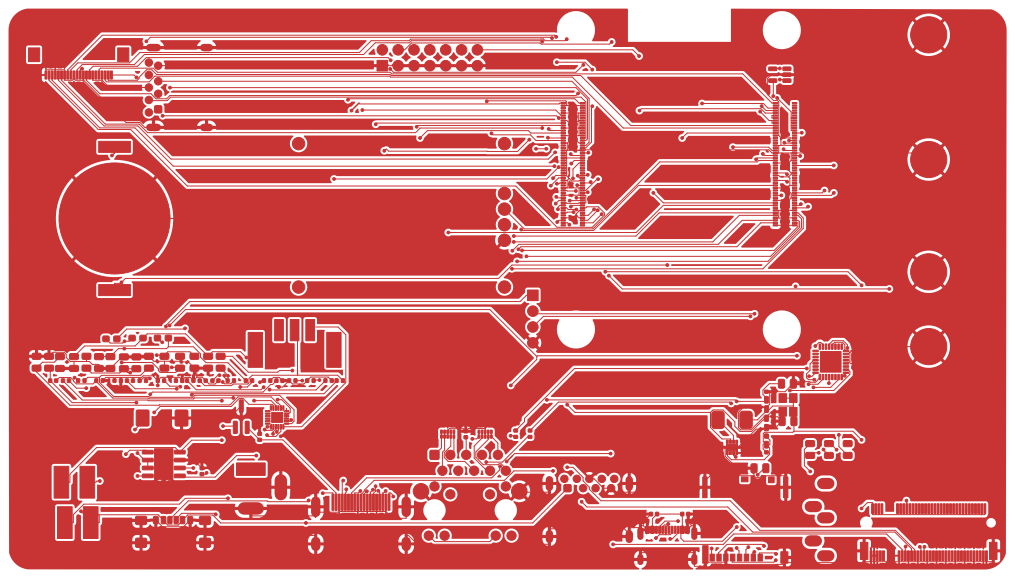
[picture p174: page 1]

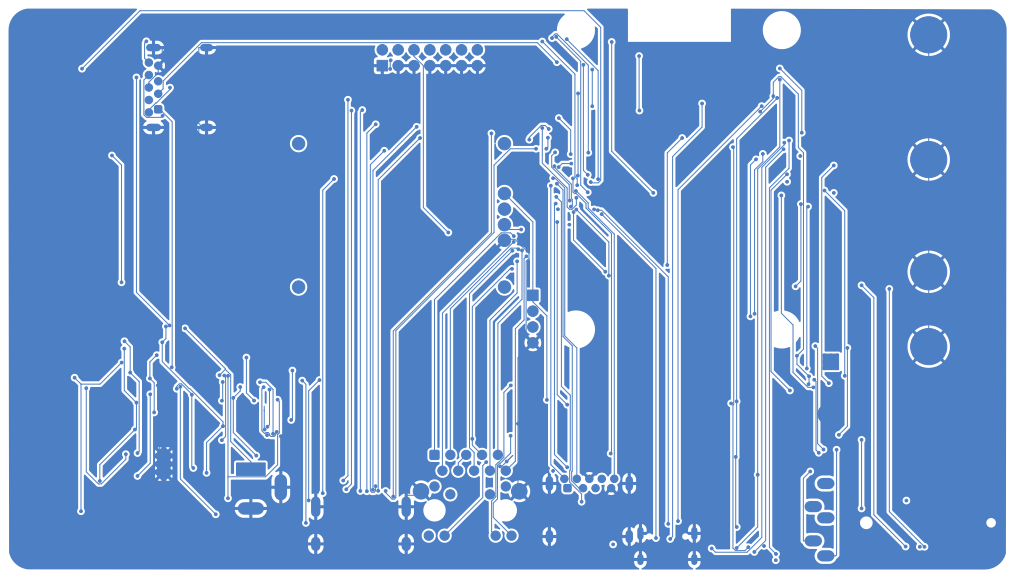
[picture p175: page 2]

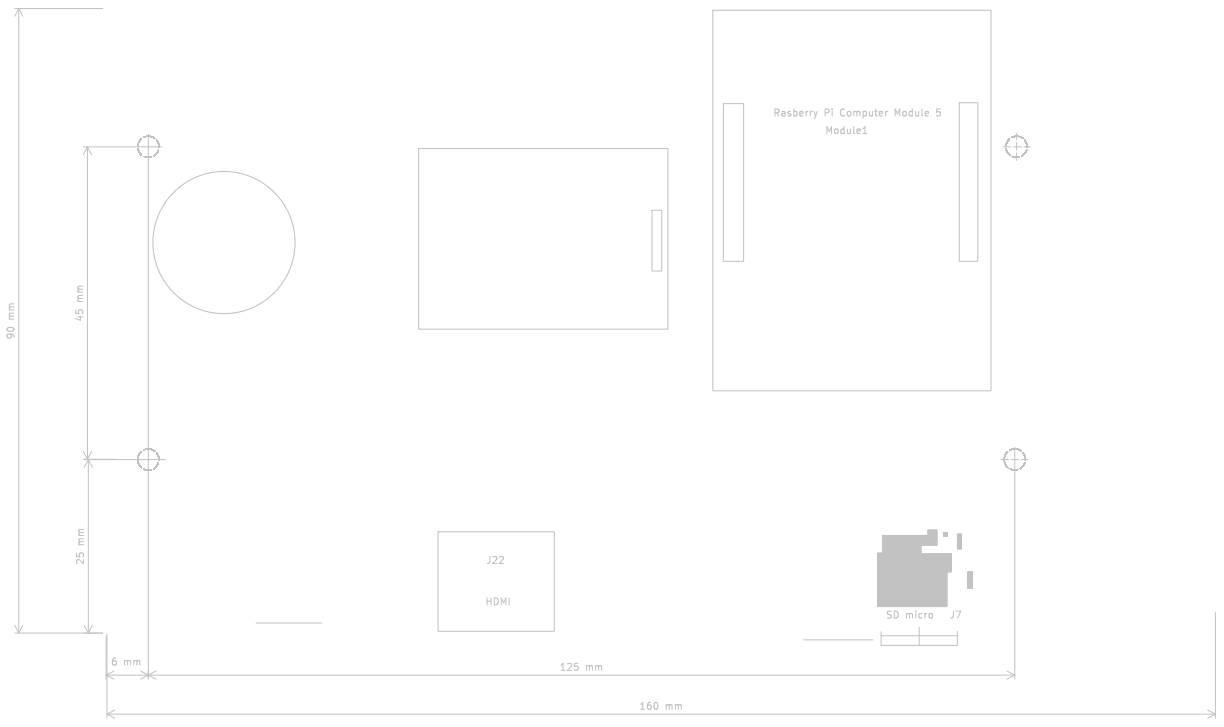
[picture p176: page 3]

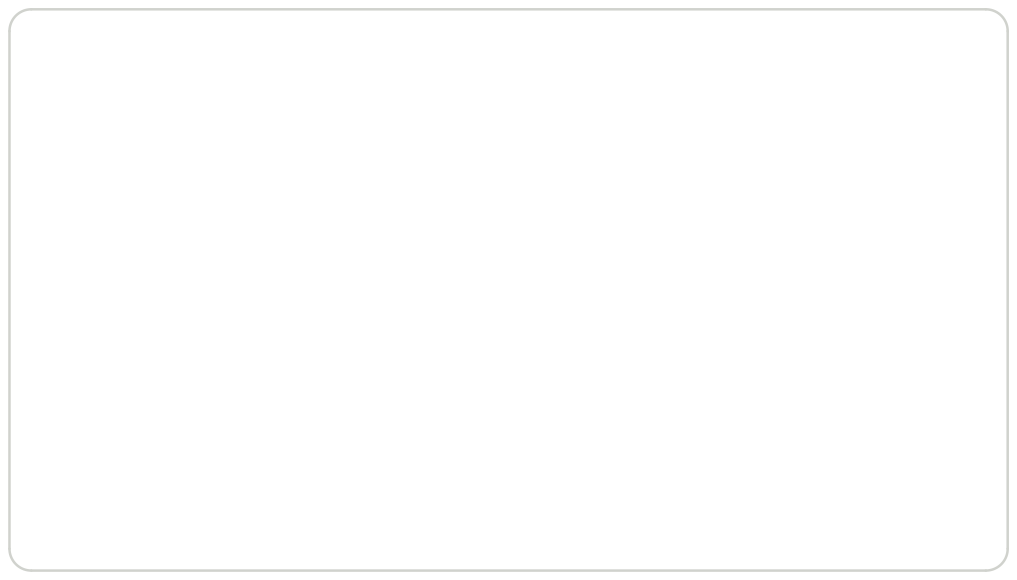
[picture p177: page 4]

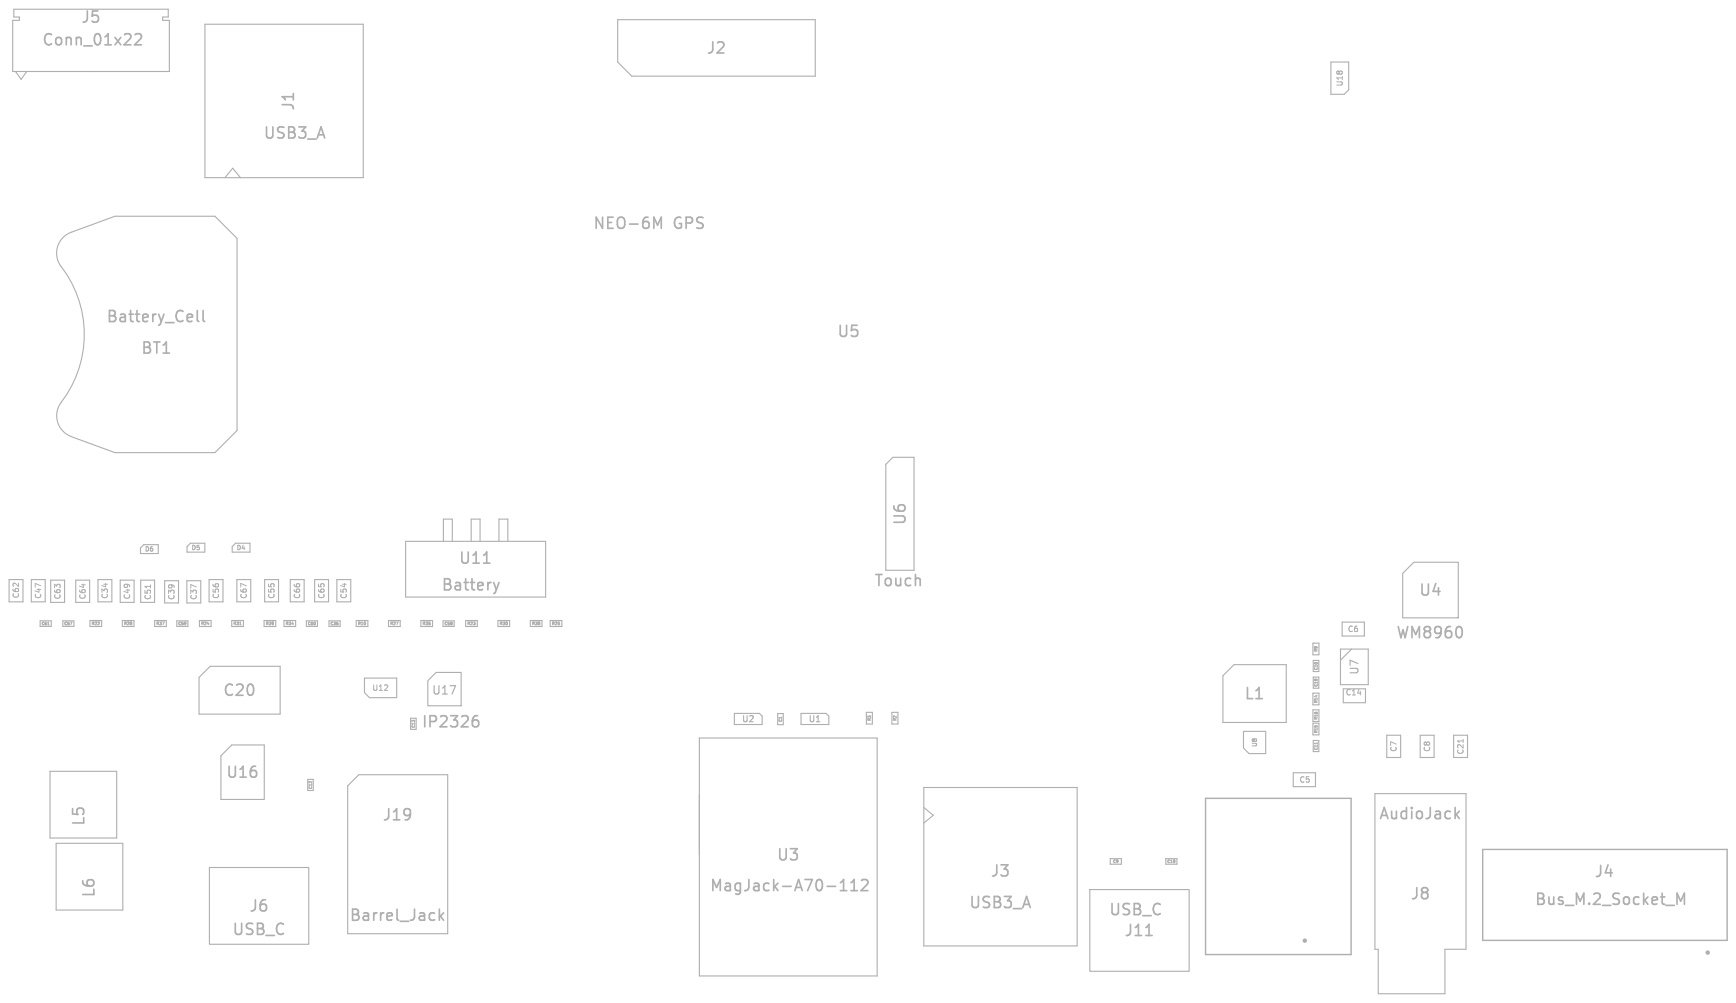
[picture p178: page 5]
