BogdanBackend/Diplom/motherBoard/Out/pcb/PCB.pdf

# J11 U¹⁸

# Вид спереду

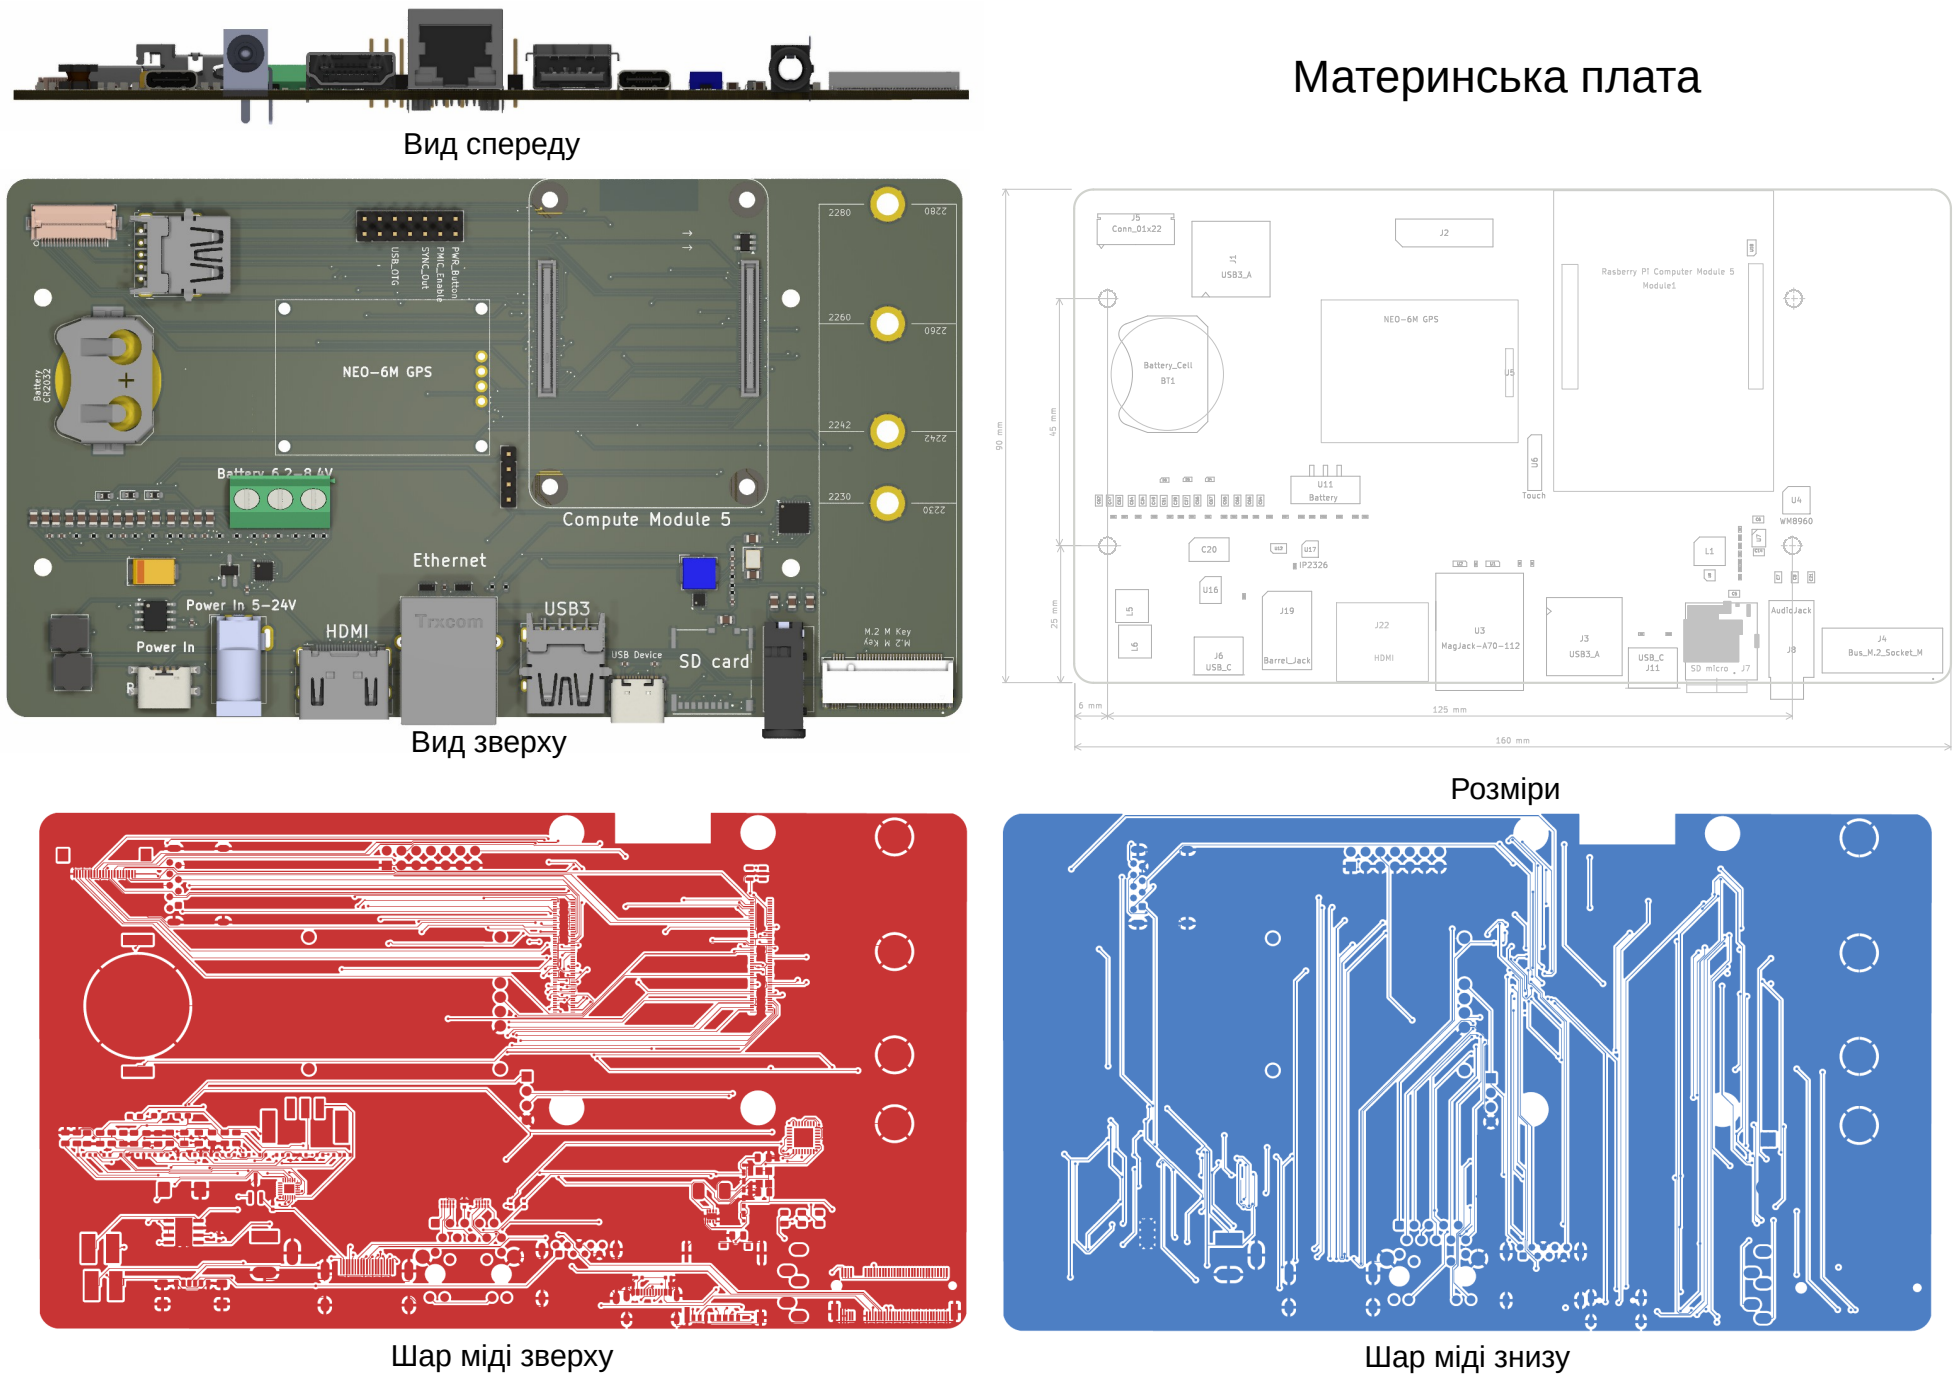
[picture p179: page 1]
