BogdanBackend/Diplom/motherBoard/Out/pcb/all/CM5IO.pdf

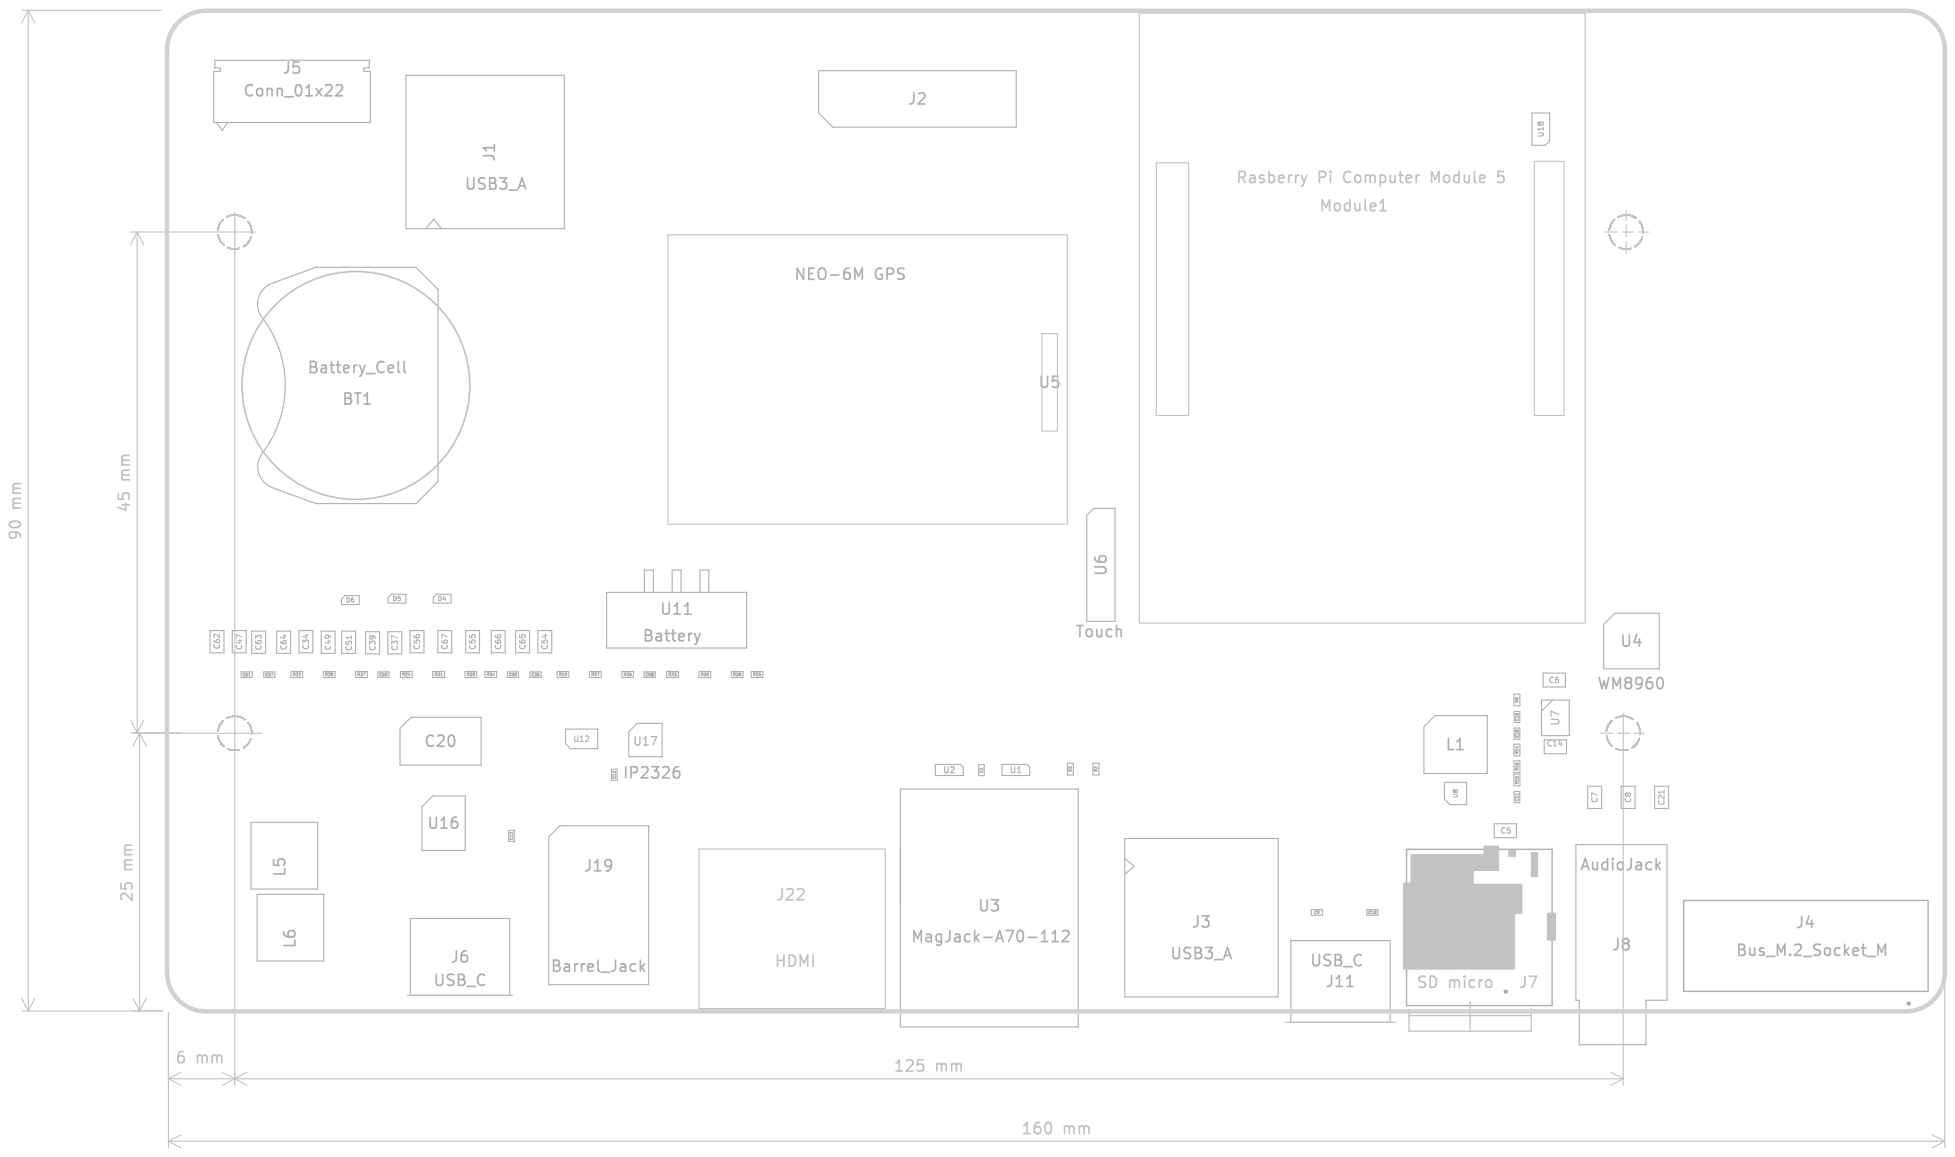
[picture p180: page 1]
